sophondroplet/Camera_gimbal_project/Software/STM32G431CUB6_firmware/gorgon test.ioc

Mcu.UserName=STM32G431CBUx
PA10.Signal=S_TIM1_CH3
PA12.Signal=TIM1_CH2N
PA15.Signal=S_TIM2_CH1
PA8.Signal=S_TIM1_CH1
PA9.Signal=S_TIM1_CH2
PB12.Signal=ADC1_IN11
PB15.Signal=TIM1_CH3N
PB3.Signal=USART2_TX
PB4.Signal=USART2_RX
PB6.GPIO_Label=IMU_INT
PB6.Signal=GPIO_Input
PB7.Signal=I2C1_SDA
PB8-BOOT0.Signal=I2C1_SCL
PC13.Signal=TIM1_CH1N
PC6.Signal=GPIO_Output
PF0-OSC_IN.Signal=RCC_OSC_IN
PF1-OSC_OUT.Signal=RCC_OSC_OUT
